oguzhanbaser/NeuroSky-Race/Web-Interface/img/green.png

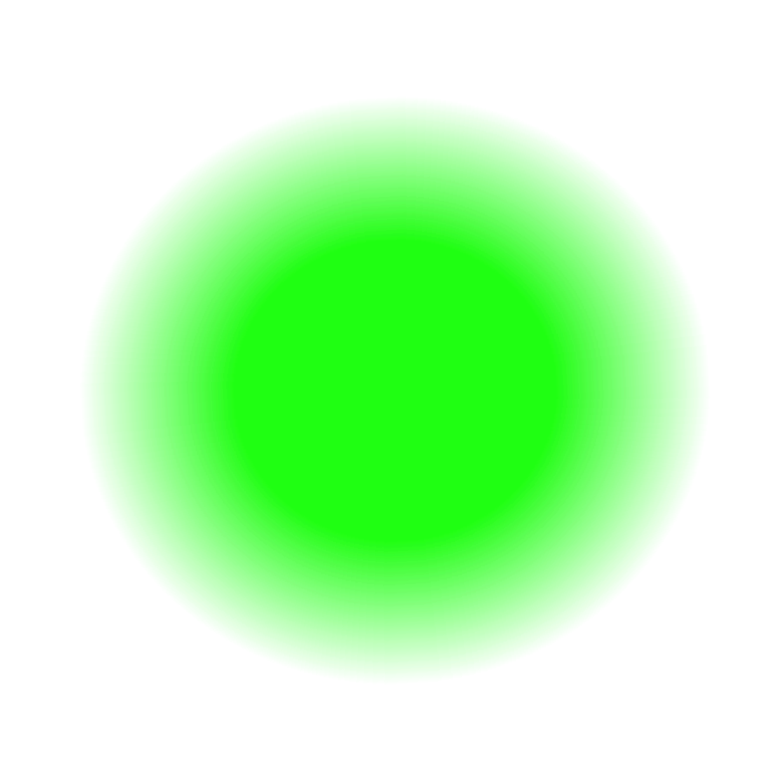
Web-Interface/img/green.png
